krakrukra/PocketAdmin/extra/payloads/KeyScreenSpyware/klog-src/vkmap.h

static unsigned int VKmapNoShift_0409[64] =
{
  //-----keyboard digits------
  '0',//VKcode = 0x30
  '1',
  '2',
  '3',
  '4',
  '5',
  '6',
  '7',
  '8',
  '9',//VKcode = 0x39
  //-----keyboard letters------
  'a',//VKcode = 0x41
  'b',
  'c',
  'd',
  'e',
  'f',
  'g',
  'h',
  'i',
  'j',
  'k',
  'l',
  'm',
  'n',
  'o',
  'p',
  'q',
  'r',
  's',
  't',
  'u',
  'v',
  'w',
  'x',
  'y',
  'z',//VKcode = 0x5A
  //-------keypad------
  '0',//VKcode = 0x60
  '1',
  '2',
  '3',
  '4',
  '5',
  '6',
  '7',
  '8',
  '9',
  '*',
  '+',
  0x00,
  '-',
  '.',
  '/',//VKcode = 0x6F
  //---------keyboard punctuation marks--------
  ';',//VKcode = 0xBA
  '=',
  ',',
  '-',
  '.',
  '/',
  '`',//VKcode = 0xC0
  //---------keyboard punctuation marks--------
  '[',//VKcode = 0xDB
  '\\',
  ']',
  '\'',//VKcode = 0xDE
  0x00//VKcode = 0xDF
};

static unsigned int VKmapWithShift_0409[64] =
{
  //----- keyboard digits ------
  ')',//VKcode = 0x30
  '!',
  '@',
  '#',
  '$',
  '%',
  '^',
  '&',
  '*',
  '(',//VKcode = 0x39
  //----- keyboard letters ------
  'A',//VKcode = 0x41
  'B',
  'C',
  'D',
  'E',
  'F',
  'G',
  'H',
  'I',
  'J',
  'K',
  'L',
  'M',
  'N',
  'O',
  'P',
  'Q',
  'R',
  'S',
  'T',
  'U',
  'V',
  'W',
  'X',
  'Y',
  'Z',//VKcode = 0x5A
  //------- keypad ------
  0x00,//VKcode = 0x60
  0x00,
  0x00,
  0x00,
  0x00,
  0x00,
  0x00,
  0x00,
  0x00,
  0x00,
  '*',
  '+',
  0x00,
  '-',
  0x00,
  '/',//VKcode = 0x6F
  //--------- keyboard punctuation marks --------
  ':',//VKcode = 0xBA
  '+',
  '<',
  '_',
  '>',
  '?',
  '~',//VKcode = 0xC0
  //--------- keyboard punctuation marks --------
  '{',//VKcode = 0xDB
  '|',
  '}',
  '"',//VKcode = 0xDE
  0x00//VKcode = 0xDF
};

static unsigned int VKmapNoShift_0419[64] =
{
  //----- keyboard digits ------
  '0',//VKcode = 0x30
  '1',
  '2',
  '3',
  '4',
  '5',
  '6',
  '7',
  '8',
  '9',//VKcode = 0x39
  //----- keyboard letters ------
  0x84D1,//VKcode = 0x41
  0xB8D0,
  0x81D1,
  0xB2D0,
  0x83D1,
  0xB0D0,
  0xBFD0,
  0x80D1,
  0x88D1,
  0xBED0,
  0xBBD0,
  0xB4D0,
  0x8CD1,
  0x82D1,
  0x89D1,
  0xB7D0,
  0xB9D0,
  0xBAD0,
  0x8BD1,
  0xB5D0,
  0xB3D0,
  0xBCD0,
  0x86D1,
  0x87D1,
  0xBDD0,
  0x8FD1,//VKcode = 0x5A
  //------- keypad ------
  '0',//VKcode = 0x60
  '1',
  '2',
  '3',
  '4',
  '5',
  '6',
  '7',
  '8',
  '9',
  '*',
  '+',
  0x00,
  '-',
  '.',
  '/',//VKcode = 0x6F
  //--------- keyboard punctuation marks --------
  0xB6D0,//VKcode = 0xBA
  '=',
  0xB1D0,
  '-',
  0x8ED1,
  '.',
  0x91D1,//VKcode = 0xC0
  //--------- keyboard punctuation marks --------
  0x85D1,//VKcode = 0xDB
  '\\',
  0x8AD1,
  0x8DD1,//VKcode = 0xDE
  0x00//VKcode = 0xDF
};

static unsigned int VKmapWithShift_0419[64] =
{
  //----- keyboard digits ------
  ')',//VKcode = 0x30
  '!',
  '"',
  0x9684E2,
  ';',
  '%',
  ':',
  '?',
  '*',
  '(',//VKcode = 0x39
  //----- keyboard letters ------
  0xA4D0,//VKcode = 0x41
  0x98D0,
  0xA1D0,
  0x92D0,
  0xA3D0,
  0x90D0,
  0x9FD0,
  0xA0D0,
  0xA8D0,
  0x9ED0,
  0x9BD0,
  0x94D0,
  0xACD0,
  0xA2D0,
  0xA9D0,
  0x97D0,
  0x99D0,
  0x9AD0,
  0xABD0,
  0x95D0,
  0x93D0,
  0x9CD0,
  0xA6D0,
  0xA7D0,
  0x9DD0,
  0xAFD0,//VKcode = 0x5A
  //------- keypad ------
  0x00,//VKcode = 0x60
  0x00,
  0x00,
  0x00,
  0x00,
  0x00,
  0x00,
  0x00,
  0x00,
  0x00,
  '*',
  '+',
  0x00,
  '-',
  0x00,
  '/',//VKcode = 0x6F
  //--------- keyboard punctuation marks --------
  0x96D0,//VKcode = 0xBA
  '+',
  0x91D0,
  '_',
  0xAED0,
  ',',
  0x81D0,//VKcode = 0xC0
  //--------- keyboard punctuation marks --------
  0xA5D0,//VKcode = 0xDB
  '/',
  0xAAD0,
  0xADD0,//VKcode = 0xDE
  0x00//VKcode = 0xDF
};
